dijkstrw/leather/fountainpen/artwork/Pelikan.png

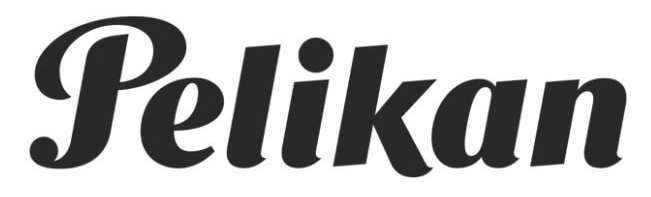
fountainpen/artwork/Pelikan.png
